Valeria/eRos-Psyche/Images/blynkDirect.jpg

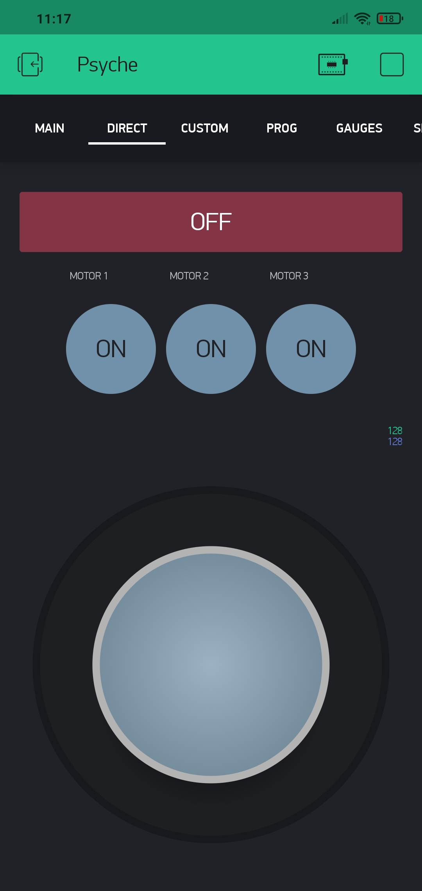
Images/blynkDirect.jpg
