Valeria/eRos-Psyche/Psyche/include/asyncSetup.h

/*// Use button V10 (BLYNK_PIN_FORCED_CONFIG) to enter forced Config Portal
BLYNK_WRITE(BLYNK_PIN_FORCED_CONFIG)
{ 
  if (param.asInt())
  {
    Serial.println( F("\nCP Button Hit. Rebooting") ); 

    // This will keep CP once, clear after reset, even you didn't enter CP at all.
    Blynk.resetAndEnterConfigPortal(); 
  }
}
*/
void set_led(byte status)
{
  digitalWrite(LED_BUILTIN, status);
}

void noticeAlive(void)
{
  if (USE_BLE)
    Blynk_BLE.virtualWrite(V0, F("OK"));
  else
    Blynk_WF.virtualWrite(V0, F("OK"));
}

void heartBeatPrint(void)
{
  static int num = 1;

  if (Blynk.connected())
  {
    set_led(HIGH);
    led_ticker.once_ms(111, set_led, (byte)LOW);
    Serial.print(F("B"));
  }
  else
  {
    Serial.print(F("F"));
  }

  if (num == 80)
  {
    Serial.println();
    num = 1;
  }
  else if (num++ % 10 == 0)
  {
    Serial.print(F(" "));
  }
}

void checkStatus()
{
  static unsigned long checkstatus_timeout = 0;

#define STATUS_CHECK_INTERVAL 60000L

  // Send status report every STATUS_REPORT_INTERVAL (60) seconds: we don't need to send updates frequently if there is no status change.
  if ((millis() > checkstatus_timeout) || (checkstatus_timeout == 0))
  {
    if (!USE_BLE)
    {
      // report Blynk connection
      heartBeatPrint();
    }

    checkstatus_timeout = millis() + STATUS_CHECK_INTERVAL;
  }
}

char BLE_Device_Name[] = "eRos Board V0.1";

#if USING_CUSTOMS_STYLE
const char NewCustomsStyle[] /*PROGMEM*/ = "<style>div,input{padding:5px;font-size:1em;}input{width:95%;}body{text-align: center;}\
button{background-color:blue;color:white;line-height:2.4rem;font-size:1.2rem;width:100%;}fieldset{border-radius:0.3rem;margin:0px;}</style>";
#endif
